LauanMath/kaelix-firmware/docs/referencias.md

# Referências — revisão de literatura do Kaelix

Levantamento gerado por busca sistemática em 5 eixos temáticos, confrontando os
achados numéricos do projeto com a literatura publicada.

> **Estado de verificação.** A etapa de auditoria independente das citações **não
> chegou a rodar** (limite de sessão). A coluna *Meta* traz a confiança auto-declarada
> pelo agente de busca. As entradas marcadas **[CONFERIDO]** foram verificadas por mim
> em fonte primária. Antes de citar qualquer item deste documento na monografia,
> confirme autores, ano e veículo no site do editor ou no DOI.

---

## Verificações em fonte primária

Conferi as citações de maior peso. Duas apresentavam problemas.

### ✅ Vieira, Bauler, Rosa, Silva (2026) — números corrigidos

*Towards a more realistic evaluation of machine learning models for bearing fault
diagnosis.* Mechanical Systems and Signal Processing, v. 258, art. 114640 (no prelo).
Preprint: [arXiv:2509.22267](https://arxiv.org/abs/2509.22267).

**Atenção: há duas versões do artigo com numeração de tabelas diferente.** Verifiquei a
**v1** (set/2025) e o agente de busca leu a **v5** (jul/2026, que é a versão aceita).

Na **v1, Tabela 12** (modelo WDCNN), que eu li diretamente:

| Protocolo no CWRU | Domínio do tempo | Domínio da frequência |
|---|---|---|
| Sem vazamento (*bearing-wise*) | 66,4% ± 16,8% | 62,4% ± 20,6% |
| Vazamento de rolamento (*condition-wise*) | 99,9% ± 0,2% | 100,0% ± 0,0% |
| Vazamento de segmentação | 99,8% ± 0,2% | 99,9% ± 0,1% |

A v1 **não traz p-valores** e **não tem Tabela 13**.

O agente cita a **v5, Tabela 13**: 63,17% ± 10,84% (tempo), 64,34% ± 9,29% (frequência),
63,89% ± 9,26% (envelope) sem vazamento, contra 100,00% ± 0,00% com vazamento
*condition-wise*, e p = 7,11e-8. A v5 reorganizou o artigo (o vazamento virou a Seção 6),
então essa tabela plausivelmente existe — **não consegui confirmá-la** porque o HTML da
v5 veio truncado antes da Seção 6.

**Encaminhamento:** ambas as versões apontam a mesma conclusão — inflação de **33 a 37
pontos percentuais**, contra os 35,8 que medimos (99,0% → 63,2%). Antes de citar na
monografia, **baixe a versão publicada em MSSP** e confirme tabela, valores e p-valor.
Não cite os dois conjuntos de números como se fossem do mesmo lugar.

### ⚠️ El Bouharrouti, Moríñigo-Sotelo, Belahcen (2024) — rótulo invertido

*Multi-Rate Vibration Signal Analysis for Bearing Fault Detection in Induction Machines
Using Supervised Learning Classifiers.* Machines (MDPI), v. 12, n. 1, art. 17.
DOI: 10.3390/machines12010017.

O agente classificou como **"contradiz"** o nosso A1. Li o PDF: **o paper apoia o A1.**
A Figura 7 mostra acurácia baixa a 1 kHz, subindo acentuadamente a partir de 12 kHz, e o
texto afirma que a melhora ocorre "particularmente para sinais cuja taxa é igual ou
superior a 12 kHz". SVM e MNLR "não aprenderam do conjunto de treino" a 1 e 6 kHz. Na
Figura 9, modelos treinados a 1–6 kHz classificam mal os sinais de 48 kHz.

Três ressalvas que **enfraquecem o paper como evidência**, em qualquer direção:

1. **Confundidor de quantidade de dados.** A 1 kHz restam 96 amostras contra 4678 a
   48 kHz (Figura 6). O colapso pode ser escassez de dados, não perda de banda.
2. **Falhas artificiais por eletroerosão**, de 0,178 a 0,533 mm — severas, não
   incipientes. Não testa o caso que nos interessa.
3. **Batches com 50% de sobreposição**, sem split por rolamento — exatamente o
   vazamento que o item A3 identifica. Os valores absolutos são provavelmente inflados.

Usam 20 descritores de domínio do tempo (incluindo curtose e fator de crista) e
**descartaram explicitamente os descritores de frequência**.

### ✅ Demais verificações pontuais

- **ISO 20816-3:2022 e ISO 10816-3:2009** — o agente afirma ter lido o texto normativo e
  cita a exigência de resposta plana em 10–1000 Hz. Plausível e coerente com a ISO 2954,
  mas **não confirmei o texto da norma** (documento pago). Confirme antes de citar.
- **Documentação do scikit-learn** — a afirmação de que `offset_ = -0.5` quando
  `contamination="auto"` é verificável na documentação oficial e sustenta o A4.

---

## Eixo 1 — Isolation Forest, limiar e TinyML embarcado

**Achado confrontado:** A4 · **Veredito da busca:** ALINHADO

| Paper | Ano | Veículo | Relação | Meta |
|---|---|---|---|---|
| Antonini, Pincheira, Vecchio, Antonelli. *An Adaptable and Unsupervised TinyML Anomaly Detection System for Extreme Indust* | 2023 | Sensors (MDPI), 23(4):2344 | confirma | ✓ |
| scikit-learn developers. *sklearn.ensemble.IsolationForest -- documentacao oficial (v1.9 estavel, acessada* | 2026 | Documentacao oficial scikit-learn (fonte prim | confirma | ✓ |
| Liu, Ting, Zhou. *Isolation Forest* | 2008 | IEEE ICDM 2008, pp. 413-422 | matiza | ✓ |
| Ma, Zhao, Zhang, Akoglu. *The Need for Unsupervised Outlier Model Selection: A Review and Evaluation of In* | 2021 | arXiv cs.LG 2104.01422; versao de revista em  | confirma | ✓ |
| Han, Hu, Huang, Jiang, Zhao. *ADBench: Anomaly Detection Benchmark* | 2022 | NeurIPS 2022 (Datasets & Benchmarks Track) | matiza | ✓ |
| Brito, Susto, Brito, Duarte. *An Explainable Artificial Intelligence Approach for Unsupervised Fault Detection* | 2021 | arXiv cs.AI 2102.11848 (versao de revista: Me | confirma | ~ |
| Hermansa, Kozielski, Michalak, Szczyrba, Wrobel, Sikora. *Sensor-Based Predictive Maintenance with Reduction of False Alarms -- A Case Stu* | 2022 | Sensors (MDPI), 22(1):226 | confirma | ✓ |
| Barbariol, Susto. *TiWS-iForest: Isolation forest in weakly supervised and tiny ML scenarios* | 2022 | Information Sciences, 610:126-143 | matiza | ✓ |
| Siffer, Fouque, Termier, Largouet. *Anomaly Detection in Streams with Extreme Value Theory* | 2017 | ACM SIGKDD (KDD) 2017, pp. 1067-1075 | matiza | ✓ |
| Koizumi, Kawaguchi, Imoto, Nakamura, Nikaido, Tanabe, Purohi. *Description and Discussion on DCASE2020 Challenge Task2: Unsupervised Anomalous * | 2020 | DCASE2020 Workshop (arXiv 2006.05822) | matiza | ✓ |
| Bouman, Bukhsh, Heskes. *Unsupervised Anomaly Detection Algorithms on Real-world Data: How Many Do We Nee* | 2024 | Journal of Machine Learning Research, 25(105) | contexto | ✓ |
| Bouman, Heskes. *Autoencoders for Anomaly Detection are Unreliable* | 2025 | arXiv cs.LG 2501.13864 (preprint, sem publica | contexto | ✓ |

<details><summary>Achados detalhados</summary>

**Antonini, Pincheira, Vecchio, Antonelli (2023)** — An Adaptable and Unsupervised TinyML Anomaly Detection System for Extreme Industrial Environments  
`https://doi.org/10.3390/s23042344`  
Trabalho mais proximo do Kaelix: Isolation Forest TREINADO E EXECUTADO no proprio ESP32 (ESP32_WROVER_IE, firmware MicroPython), amostragem de acel+giro a 1125 Hz. Numeros: 84 KB de memoria na inferencia com ensemble de 50 arvores; ~1.570 KB no treino com 30 arvores; carregamento do modelo ate ~1 MB para 50 arvores; latencia de inferencia 20,33 +/- 7,17 ms (instancias normais) e 16,27 +/- 7,04 ms (anomalas); treino on-device 1,2-6,4 s para 10-50 arvores. PONTO CRITICO PARA A4: o limiar de deteccao NAO foi deixado no default -- foi FIXADO MANUALMENTE em 0,75 sobre o score normalizado do Isolation Forest, assumindo que a fase inicial de treino contem apenas comportamento normal. Os autores declaram explicitamente que avaliar a acuracia de deteccao esta fora do escopo do trabalho -- ou seja, nao ha FPR reportado.

**scikit-learn developers (2026)** — sklearn.ensemble.IsolationForest -- documentacao oficial (v1.9 estavel, acessada em ago/2026)  
`https://scikit-learn.org/stable/modules/generated/sklearn.ensemble.IsolationForest.html`  
PROVA MECANICA DIRETA DE A4. Texto literal do atributo offset_: 'decision_function = score_samples - offset_. When the contamination parameter is set to "auto", the offset is equal to -0.5 as the scores of inliers are close to 0 and the scores of outliers are close to -1. When a contamination parameter different than "auto" is provided, the offset is defined in such a way we obtain the expected number of outliers (samples with decision function < 0) in training.' Consequencias: (1) contamination='auto' congela o corte em -0,5, um valor herdado da interpretacao do artigo original, NAO calibrado nos dados -- por isso pode marcar fracao arbitrariamente grande da operacao normal; (2) contamination altera SOMENTE o offset, nunca os scores brutos de score_samples -- logo qualquer metrica baseada em ranking (ROC-AUC) e matematicamente INVARIANTE ao parametro. Isso confirma exatamente o achado 'AUC=1,000 independente do parametro: ele so move o limiar'. Range permitido para float: (0, 0.5].

**Liu, Ting, Zhou (2008)** — Isolation Forest  
`https://doi.org/10.1109/ICDM.2008.17`  
Artigo fundador. Score s(x,n) = 2^(-E(h(x))/c(n)), com c(n) o comprimento medio de caminho em uma BST aleatoria de n nos. s -> 1 indica anomalia; s -> 0 indica normal denso; s ~ 0,5 corresponde a E(h(x)) ~ c(n), ou seja, ponto com profundidade tipica. Os autores usam 0,5 como REFERENCIA INTERPRETATIVA (se toda a amostra devolve s ~ 0,5, o conjunto nao tem anomalia distinta), nao como limiar operacional calibrado -- e exatamente esse 0,5 que o sklearn materializa como offset_=-0,5 no modo 'auto'. Defaults recomendados de ensemble: t=100 arvores, psi=256 (subamostragem), que os autores mostram ser robustos -- a robustez do iForest e nos parametros do ENSEMBLE, nao no limiar.

**Ma, Zhao, Zhang, Akoglu (2021)** — The Need for Unsupervised Outlier Model Selection: A Review and Evaluation of Internal Evaluation Strategies (A Large-scale Study on Unsupervised Outlier Model Selection: Do Internal Strategies Suffice?)  
`https://arxiv.org/abs/2104.01422`  
Responde diretamente a pergunta 'como escolher contamination sem rotulos'. Testbed com 39 tarefas de deteccao, 297 modelos candidatos (8 detectores x varias configuracoes de hiperparametros) e 7 estrategias internas de avaliacao (sem rotulos). Conclusao literal: nenhuma seria 'practically useful, as they select models only comparable to a state-of-the-art detector (with random configuration)'. Ou seja: NAO existe metodo label-free confiavel para escolher detector+hiperparametro; deixar no default e estatisticamente equivalente a sortear -- o que valida a critica de A4 ao contamination='auto' como escolha nao informada.

**Han, Hu, Huang, Jiang, Zhao (2022)** — ADBench: Anomaly Detection Benchmark  
`https://arxiv.org/abs/2206.09426`  
30 algoritmos (14 nao supervisionados, 7 semi-supervisionados, 9 supervisionados) x 57 datasets = 98.436 experimentos. Dois achados diretamente aplicaveis: (1) NENHUM algoritmo nao supervisionado e estatisticamente melhor que os outros -- a escolha do detector importa menos que o protocolo; (2) com apenas 1% de anomalias ROTULADAS, a maioria dos metodos semi-supervisionados ja supera o melhor metodo nao supervisionado. Implicacao pratica para o Kaelix: rotular alguns ensaios de falha (ex.: MAFAULDA) produz mais resultado que otimizar o Isolation Forest puro.

**Brito, Susto, Brito, Duarte (2021)** — An Explainable Artificial Intelligence Approach for Unsupervised Fault Detection and Diagnosis in Rotating Machinery  
`https://arxiv.org/abs/2102.11848`  
11 detectores nao supervisionados comparados (kNN, MCD, LOF, CBLOF, OCSVM, Descritor Bagging, FastABOD, Isolation Forest, HBOS, LODA, Ensemble) em 3 datasets de maquinas rotativas, com descritores de vibracao a 20 kHz (curtose, RMS, BPFI/BPFO/BSF, harmonicos 1x-4x) e explicabilidade via SHAP e Local-DIFFI. Numeros: IF com F1 97,19% e PR-AUC 99,92% (rolamento run-to-failure), F1 99,71% e PR-AUC 99,99% (caixa de engrenagens), F1 97,20% e PR-AUC 99,74% (faltas mecanicas). PONTO CRITICO: o limiar NAO veio de 'auto' -- em condicao estatica a razao de contaminacao era CONHECIDA e usada para definir o limiar; em condicao dinamica o limiar veio da hipotese 'o grupo de treino contem apenas sinais normais'. Alem disso reportam PR-AUC, nao so ROC-AUC.

**Hermansa, Kozielski, Michalak, Szczyrba, Wrobel, S (2022)** — Sensor-Based Predictive Maintenance with Reduction of False Alarms -- A Case Study in Heavy Industry  
`https://doi.org/10.3390/s22010226`  
Melhor evidencia de campo sobre taxa de falso alarme. Comparam HDBSCAN, LOF, Isolation Forest e One-Class SVM em sensores de vibracao (max e RMS) + temperatura de britadores de carvao (NW-10, NW-20) e porticos (S201, S202), mais um dataset sintetico de 30.000 observacoes. Numeros: o detector de outliers ISOLADO produziu metrica de falso positivo N entre 0,457 e 0,939 conforme o conjunto; adicionando adaptacao do modelo base + modelo de correcao, N caiu para 0,026-0,115, uma reducao MEDIA de 90,25% nos falsos alarmes. Ou seja: um detector nao supervisionado 'cru' e inaceitavel em campo, exatamente o cenario de A4.

**Barbariol, Susto (2022)** — TiWS-iForest: Isolation forest in weakly supervised and tiny ML scenarios  
`https://doi.org/10.1016/j.ins.2022.07.129`  
Unico trabalho encontrado que ataca o Isolation Forest especificamente para TinyML/microprocessadores ultra-restritos. Argumento central: 'the standard algorithm might be improved in terms of memory requirements, latency and performances', o que e critico em cenarios de baixo recurso e implementacoes TinyML. A solucao proposta NAO e mexer em contamination, e sim usar supervisao FRACA (poucos rotulos) para ranquear e podar as arvores do ensemble, reduzindo simultaneamente memoria, latencia e erro de deteccao. Codigo publico para reprodutibilidade. Preprint anterior: arXiv 2111.15432 (2021).

**Siffer, Fouque, Termier, Largouet (2017)** — Anomaly Detection in Streams with Extreme Value Theory  
`https://doi.org/10.1145/3097983.3098144`  
Alternativa metodologica principiada ao contamination. Os algoritmos SPOT/DSPOT usam Teoria de Valores Extremos (peaks-over-threshold / distribuicao de Pareto generalizada) para fixar o limiar SEM hipotese sobre a distribuicao dos dados e SEM limiar ajustado a mao. O unico parametro e o RISCO q, que controla diretamente a taxa de falsos positivos -- isto e, o engenheiro especifica o FPR desejado em vez de adivinhar a fracao de anomalias. E exatamente a substituicao que A4 pede para contamination='auto'.

**Koizumi, Kawaguchi, Imoto, Nakamura, Nikaido, Tana (2020)** — Description and Discussion on DCASE2020 Challenge Task2: Unsupervised Anomalous Sound Detection for Machine Condition Monitoring  
`https://arxiv.org/abs/2006.05822`  
Benchmark de referencia para o cenario EXATO do Kaelix: so ha dados normais no treino e as anomalias sao desconhecidas ('detect unknown anomalous sounds under the condition that only normal sound samples have been provided as training data'). 117 submissoes de 40 equipes. PROTOCOLO DE LIMIAR (o que substituir por contamination='auto'): o baseline autoencoder assume que o score de anomalia segue uma distribuicao GAMA, estima os parametros a partir do histograma dos scores dos dados NORMAIS de treino e define o limiar no PERCENTIL 90 dessa gama. Metrica primaria e AUC + pAUC (AUC parcial em faixa de baixa FPR), justamente porque AUC global sozinha nao caracteriza o ponto de operacao.

</details>

**Números citáveis:** MECANISMO (scikit-learn, doc oficial v1.9): contamination='auto' => offset_ = -0.5; decision_function = score_samples - offset_; float permitido apenas em (0, 0.5]; contamination redefine SO o offset, nunca score_samples => ROC-AUC invariante. | LIU/TING/ZHOU 2008 (ICDM, pp. 413-422): s(x,n)=2^(-E(h(x))/c(n)); s~0.5 <=> E(h(x))~c(n); defaults de ensemble t=100 arvores, psi=256 subamostras. | ANTONINI 2023 (Sensors 23(4):2344, ESP32 + IF em MicroPython): amostragem 1125 Hz; 84 KB de RAM na inferencia com 50 arvores; ~1.570 KB no treino com 30 arvores; carregamento de modelo ate ~1 MB (50 arvores); latencia 20,33 +/- 7,17 ms (normal) e 16,27 +/- 7,04 ms (anomalo); treino on-device 1,2-6,4 s (10-50 arvores); LIMIAR FIXADO EM 0,75 do score normalizado. | HERMANSA 2022 (Sensors 22(1):226): detector isolado com metrica de FP N = 0,457-0,939; com adaptacao+correcao N = 0,026-0,115; reducao media de falsos alarmes de 90,25%; dataset sintetico de 30.000 observacoes. | BRITO/SUSTO (MSSP 163:108105 / arXiv 2102.11848): 11 detectores; sinais a 20 kHz; IF F1 97,19% e PR-AUC 99,92% (rolamento), F1 99,71% e PR-AUC 99,99% (engrenagens), F1 97,20% e PR-AUC 99,74% (faltas mecanicas). | MA/AKOGLU: 39 tarefas, 297 modelos, 8 detectores, 7 estrategias internas, ZERO melhores que configuracao aleatoria. | ADBENCH (NeurIPS 2022): 30 algoritmos, 57 datasets, 98.436 experimentos; nenhum nao supervisionado estatisticamente superior; 1% de rotulos ja basta para semi-supervisionado bater o melhor nao supervisionado. | BOUMAN JMLR 2024, 25(105):1-34: 33 algoritmos x 52 datasets, EIF vence significativamente. | DCASE2020 Task 2 (Koizumi et al.): limiar = percentil 90 de uma GAMA ajustada aos scores dos dados normais de treino; metrica primaria AUC + pAUC (AUC parcial em faixa de baixa FPR); 117 submissoes de 40 equipes. | SIFFER KDD 2017 (pp. 1067-1075): SPOT/DSPOT via EVT, unico parametro = risco q que controla diretamente a taxa de falsos positivos. | REFERENCIA DE GESTAO DE ALARME (fonte NAO academica, verificar antes de citar): EEMUA 191 -- media recomendada de ~6 alarmes/hora por operador e pico de no maximo 10 alarmes por 10 minutos (inicio de 'alarm flood'); util para argumentar que 42% de janelas normais marcadas como anomalia e ordens de grandeza acima do tolerável.

**Lacunas neste eixo:** 1) NUMERO ORIGINAL SEM PRECEDENTE NA LITERATURA: nao encontrei nenhum trabalho que quantifique a FRACAO da operacao normal marcada como anomalia por contamination='auto' em vibracao industrial. Os 42% de voces parecem ser contribuicao original -- otimo para o TCC, mas exige que a metodologia (dataset, descritores, split) seja descrita com muito rigor, porque nao ha baseline publicado para comparar. 2) O trabalho mais proximo (Antonini et al., IF em ESP32) declara EXPLICITAMENTE que avaliar acuracia de deteccao esta fora do escopo -- ou seja, nao existe FPR publicado para Isolation Forest embarcado em MCU. Isso e um buraco que o Kaelix pode preencher. 3) Ninguem cruza as duas restricoes de voces ao mesmo tempo: acelerometro MEMS de banda limitada (MPU6050, Nyquist 500 Hz) + detector nao supervisionado embarcado + limiar calibrado para um FPR alvo. A literatura de vibracao usa 20-50 kHz (Brito: 20 kHz; MAFAULDA: 50 kHz), e a literatura TinyML usa banda baixa mas sem discutir o custo diagnostico dessa escolha (conexao direta com o achado A1 de voces). 4) NAO EXISTE NORMA que fixe taxa de falso alarme aceitavel para manutencao preditiva por vibracao: ISO 10816/20816 define severidade de VELOCIDADE, nao estatistica de alarme; EEMUA 191 e ISA-18.2 sao de alarmes de processo, nao de PdM. Qualquer numero de FPR aceitavel que voces adotarem precisa ser justificado por custo (razao custo de falso negativo : falso positivo, tipicamente citada como 20:1 a 100:1 em fontes de industria -- mas so achei isso em fontes NAO academicas, nao citem sem verificar). 5) Falta comparacao controlada IF vs OC-SVM vs autoencoder EM MCU com o MESMO orcamento de memoria E o MESMO protocolo de limiar; os papers comparam ou algoritmos (em PC) ou plataformas (sem controlar o limiar). 6) Nenhuma das bibliotecas de exportacao sklearn->C mais usadas (emlearn, micromlgen) documenta suporte a IsolationForest -- so a arvores/RF/SVM/NB; Antonini et al. contornaram isso implementando o IF diretamente em MicroPython. Se voces pretendem embarcar o IF, isso e um risco de implementacao que a literatura nao cobre e que vale registrar. 7) Nao encontrei nada sobre DERIVA (concept drift) do limiar do IF em motor industrial ao longo de meses -- carga, temperatura e regime mudam o score base, e nenhum dos papers de MCU faz recalibracao periodica.

---

## Eixo 2 — Vazamento de dados e avaliação em datasets de rolamento

**Achado confrontado:** A3 · **Veredito da busca:** ALINHADO

| Paper | Ano | Veículo | Relação | Meta |
|---|---|---|---|---|
| Vieira, Bauler, Rosa, Silva. *Towards a more realistic evaluation of machine learning models for bearing fault* | 2026 | Mechanical Systems and Signal Processing, v.  | confirma | ✓ |
| Hendriks, Dumond, Knox. *Towards better benchmarking using the CWRU bearing fault dataset* | 2022 | Mechanical Systems and Signal Processing, v.  | confirma | ✓ |
| Varejão, Costa, Silva, Rodrigues, Ribeiro, Varejão, Oliveira. *The similarity bias problem: What it is and how it impacts vibration based intel* | 2025 | Mechanical Systems and Signal Processing, v.  | confirma | ✓ |
| Wheat, von Mohrenschildt, Habibi, Al-Ani. *Impact of Data Leakage in Vibration Signals Used for Bearing Fault Diagnosis* | 2024 | IEEE Access, v. 12, p. 169879-169895 | confirma | ✓ |
| Abburi, Chaudhary, Ilyas, Manne, Mittal, Williams, Snaidauf,. *A Closer Look at Bearing Fault Classification Approaches* | 2023 | Annual Conference of the PHM Society, v. 15 ( | matiza | ✓ |
| Rauber, Loca, Boldt, Rodrigues, Varejão. *An experimental methodology to evaluate machine learning methods for fault diagn* | 2021 | Expert Systems with Applications, v. 167, art | confirma | ✓ |
| Matania, Cohen, Bechhoefer, Bortman. *Test-Training Leakage in Evaluation of Machine Learning Algorithms for Condition* | 2024 | PHM Society European Conference, v. 8, n. 1,  | confirma | ✓ |
| Knap, Jachymczyk, Lalik. *Leakage-Safe, Reproducible Benchmarking for Vibration-Based Fault Diagnosis* | 2026 | PHM Society European Conference, v. 9, n. 1 | confirma | ✓ |
| Smith, Randall. *Rolling element bearing diagnostics using the Case Western Reserve University da* | 2015 | Mechanical Systems and Signal Processing, v.  | contexto | ✓ |
| Zhao, Li, Wu, Sun, Wang, Yan, Chen. *Deep learning algorithms for rotating machinery intelligent diagnosis: An open s* | 2020 | ISA Transactions, v. 107, p. 224-255 | matiza | ✓ |
| Fan, Jiang, Zhang, Zheng, Lv, Han, Liang, Li, Zhang, Qian, C. *FISHER: A Foundation Model for Multi-Modal Industrial Signal Comprehensive Repre* | 2026 | IEEE Transactions on Industrial Informatics ( | confirma | ~ |
| Shamim, Nuruzzaman, Ferdus, Ahmed, Anward, Tooneer, Khan, Ho. *Leakage-Robust Evaluation and Data-Scale Sensitivity of Attention-Enhanced Multi* | 2026 | arXiv (submetido a Next Research, Elsevier) | confirma | ✓ |

<details><summary>Achados detalhados</summary>

**Vieira, Bauler, Rosa, Silva (2026)** — Towards a more realistic evaluation of machine learning models for bearing fault diagnosis  
`https://doi.org/10.1016/j.ymssp.2026.114640 (preprint: https://arxiv.org/abs/2509.22267)`  
Paper-espelho do nosso A3, com numeros quase identicos. Experimento controlado (treino FIXO, so o conjunto de teste muda, eliminando o confundidor 'menos dados de treino'). CWRU: protocolo sem vazamento da Macro AUROC 63,17% +/- 10,84% (tempo), 64,34% +/- 9,29% (frequencia), 63,89% +/- 9,26% (envelope); com vazamento de nivel de rolamento (split condition-wise) sobe para 100,00% +/- 0,00%, 99,96% +/- 0,13% e 99,79% +/- 0,54%; com vazamento de segmentacao, 100,00% nos tres casos (p entre 7,1e-8 e 1,7e-8). PU: sem vazamento 54,25% +/- 17,79% (tempo) / 61,25% (freq) / 76,98% (envelope); condition-wise +32,6 p.p. (86,88%/92,27%/87,79%); repetition-wise 98,57%/100,00%/99,99% (+44,3 p.p.); segmentacao 98,56%/100%/100%. UORED-VAFCLS: sem vazamento 87,25%/90,21%/87,34%; vazamento de rolamento +3,0/+3,9/+6,4 p.p.; vazamento de segmentacao +12,6/+9,8/+12,5 p.p. (chega a 99,88%/100,00%/99,88%). Taxonomia formal: 'segmentation-level leakage' vs 'bearing-level leakage' (este ultimo com sub-tipos condition-wise e repetition-wise). Survey: 195 artigos MSSP de 2025 recuperados, 18 analisados em detalhe - 8 (44%) usaram split aleatorio, 9 (50%) condition-wise, 1 (6%) nao especificou; citam trabalhos anteriores que reportam problemas de particao em >90% dos artigos publicados. Toy problem com 48 rolamentos: teto teorico de acuracia 90,30%, e os testes com vazamento EXCEDERAM esse teto (prova de memorizacao). NUANCE CRITICA PARA NOS: sob split correto no CWRU (Tabela 10), o Random Forest com descritores de tempo+envelope chegou a 85,06% +/- 8,92% Macro AUROC, contra 63,22% +/- 10,24% do WDCNN - modelos rasos degradam MENOS que deep learning sob particao honesta. Outra ressalva: no experimento CWRU eles tiveram de EXCLUIR todos os sinais saudaveis, pois o CWRU tem uma unica configuracao de rolamento saudavel e nao ha como fazer split bearing-wise da classe normal.

**Hendriks, Dumond, Knox (2022)** — Towards better benchmarking using the CWRU bearing fault dataset  
`https://doi.org/10.1016/j.ymssp.2021.108732`  
Paper-semente da critica moderna ao CWRU (158 citacoes no Semantic Scholar). Argumenta que o procedimento aceito de montar treino e teste com CONDICOES DE OPERACAO diferentes (0/1/2/3 hp) NAO constitui um problema real de domain shift, porque os MESMOS rolamentos fisicos aparecem nos dois conjuntos. Propoe um framework alternativo de benchmark que constroi treino e teste com conjuntos INDEPENDENTES de rolamentos. E a origem da distincao 'variacao de condicao != variacao de componente' que sustenta o nosso A3. Limitacao apontada por Vieira et al. (2026): a estrategia por tamanho de falha de Hendriks nao elimina o vazamento da classe saudavel, que continua sendo dividida por carga.

**Varejão, Costa, Silva, Rodrigues, Ribeiro, Varejão (2025)** — The similarity bias problem: What it is and how it impacts vibration based intelligent fault diagnosis  
`https://doi.org/10.1016/j.ymssp.2025.112822`  
Cunha o termo 'similarity bias' para o fenomeno que chamamos de vazamento por janela. Levantamento sistematico: de 41 estudos revisados que usam o CWRU (publicados entre 2008 e 2020), 40 empregaram desenho experimental suscetivel a esse vies - ou seja, ~97,6% da literatura CWRU daquele periodo e otimista por construcao. Compara modelos convencionais e de deep learning sob estrategia de validacao cruzada que controla o vies, e mostra quantitativamente que o similarity bias produz resultados otimistas. Grupo brasileiro (UFES), mesmo grupo do Rauber et al. (2021) que usa MAFAULDA - terminologia util e citavel em portugues/ingles.

**Wheat, von Mohrenschildt, Habibi, Al-Ani (2024)** — Impact of Data Leakage in Vibration Signals Used for Bearing Fault Diagnosis  
`https://doi.org/10.1109/ACCESS.2024.3497716`  
Quantifica o vazamento com metodos SEM modelo treinado pesado - exatamente o regime do KAELIX. Aplica 6 metodos classicos de diagnostico (PCA, SPCA e LDA combinados com analise em frequencia e analise de envelope) a 2 datasets (McMaster e Paderborn) sob 3 estrategias de particao: run-to-run, day-to-day e part-to-part. Reporta variacoes de desempenho SUPERIORES A 40 PONTOS PERCENTUAIS de acuracia dependendo apenas da estrategia de particao, expondo domain shifts nao identificados anteriormente (inclusive shift entre DIAS de aquisicao, nao so entre pecas). Recomenda protocolos melhores de desenho experimental e avaliacao. A nomenclatura run-to-run / day-to-day / part-to-part e mais granular que o nosso 'split por ensaio' e vale adotar.

**Abburi, Chaudhary, Ilyas, Manne, Mittal, Williams, (2023)** — A Closer Look at Bearing Fault Classification Approaches  
`https://arxiv.org/abs/2309.17001 | https://papers.phmsociety.org/index.php/phmconf/article/view/3473`  
Fonte de numeros diretos e NUANCE IMPORTANTE contra a magnitude do nosso A3. Classificacao multiclasse no CWRU, comparando split por rolamento vs split aleatorio: SVM+STFT cai de 0,851 (aleatorio) para 0,700 (por rolamento) de acuracia; Naive Bayes+RFFT cai de 0,858 para 0,695. No XJTU: SVM+STFT 0,988 -> 0,890; NB+RFFT 0,910 -> 0,728. Ou seja, a queda observada por eles no CWRU e de ~15 p.p., NAO ~36 p.p. como no nosso A3. Alertam explicitamente que estudos anteriores (citam nominalmente Zhao et al. 2020) usaram split aleatorio atribuindo registros do MESMO rolamento a treino, validacao e teste. Tambem defendem F-score/metricas de desbalanceamento em vez de acuracia pura, e o uso de dummy classifiers como baseline - recomendacao diretamente aplicavel ao nosso relatorio.

**Rauber, Loca, Boldt, Rodrigues, Varejão (2021)** — An experimental methodology to evaluate machine learning methods for fault diagnosis based on vibration signals  
`https://doi.org/10.1016/j.eswa.2020.114022`  
UNICO paper de metodologia de avaliacao encontrado que usa explicitamente MAFAULDA E CWRU juntos - exatamente a nossa combinacao de datasets. Estabelece um procedimento sistematico para comparar de forma justa scores experimentais de metodos de ML sobre sinais de vibracao. Afirma que o desenho experimental da maioria das publicacoes da area e enviesado, baseado em metodos de validacao inaceitavelmente simples e na reciclagem de padroes identicos no conjunto de teste que ja foram usados no treino, o que torna a classificacao uma tarefa facil. E uma das duas fontes (junto com Varejão et al. 2025) das quais Vieira et al. (2026) tiram a estatistica de problemas de particao em >90% dos artigos publicados. 93 citacoes.

**Matania, Cohen, Bechhoefer, Bortman (2024)** — Test-Training Leakage in Evaluation of Machine Learning Algorithms for Condition-Based Maintenance  
`https://doi.org/10.36001/phme.2024.v8i1.4125`  
Artigo curto e didatico, dedicado exclusivamente ao problema: em muitos trabalhos de ML para manutencao baseada em condicao, especialmente classificacao de falhas de rolamento, a separacao de exemplos entre teste e treino esta incorreta, levando a conclusao otimista sobre o desempenho do algoritmo quando o desempenho real e menor. Propoe divisao guiada por TAMANHO DE FALHA (fault-size guided splitting) aplicada a CWRU e PU. Ressalva registrada por Vieira et al. (2026): essa estrategia nao e aplicavel a datasets em que o mesmo rolamento aparece sob multiplos tamanhos de falha (ex.: UORED-VAFCLS), e no CWRU ela nao resolve a classe saudavel. Util como citacao curta e de autoridade (Bechhoefer e referencia em PHM industrial).

**Knap, Jachymczyk, Lalik (2026)** — Leakage-Safe, Reproducible Benchmarking for Vibration-Based Fault Diagnosis  
`https://doi.org/10.36001/phme.2026.v9i1.4924`  
Benchmark reprodutivel e livre de vazamento para diagnostico cross-domain, com codigo aberto (github.com/1Sensor/pdm-bench). Afirma que particao em nivel de JANELA e cenarios fonte-alvo mal definidos levam a conclusoes excessivamente otimistas. Define 6 cenarios fonte-alvo fixos com separacao treino-teste em NIVEL DE GRAVACAO (recording-level) sobre CWRU e Paderborn. Achado que nos e util como nuance: a dificuldade dos cenarios e altamente heterogenea - alguns cenarios de transferencia estao efetivamente saturados enquanto outros permanecem substancialmente mais dificeis. Isso sugere que reportar um unico numero medio (como nosso 63,2% +/- 19,2%) esconde variancia estrutural, e que o desvio-padrao alto que observamos e esperado. Tambem nota que modelos de deep learning frequentemente atingem desempenho superior mas suas conclusoes sao sensiveis a inicializacao.

**Smith, Randall (2015)** — Rolling element bearing diagnostics using the Case Western Reserve University data: A benchmark study  
`https://doi.org/10.1016/j.ymssp.2015.04.021`  
Critica FUNDACIONAL ao CWRU, anterior a discussao de ML, com 2443 citacoes. Aplica tres tecnicas classicas de diagnostico a TODO o dataset CWRU e classifica cada registro em categorias de diagnosticabilidade: Y1 (claramente diagnosticavel com caracteristicas classicas no tempo e na frequencia), Y2 (claramente diagnosticavel mas com caracteristicas nao-classicas), P1 (provavelmente diagnosticavel - componentes discretos nas frequencias de falha esperadas mas nao dominantes no espectro de envelope), P2 (potencialmente diagnosticavel - componentes borrados que parecem coincidir com as frequencias esperadas), N1 (nao diagnosticavel para a falha especificada, mas com outros problemas identificaveis como folga/looseness) e N2 (nao diagnosticavel e praticamente indistinguivel de ruido). Consequencia direta para nos: parte dos registros CWRU e ROTULADA como falha mas nao contem assinatura de falha detectavel - portanto uma acuracia de 99% em split aleatorio e literalmente impossivel por via fisica, o que e evidencia independente de que aquele numero e memorizacao. Fornece recomendacoes de como usar os dados para testar novos algoritmos.

</details>

**Números citáveis:** NUMEROS DIRETAMENTE CITAVEIS (todos extraidos de fonte primaria aberta e conferidos):

--- Vieira, Bauler, Rosa & Silva, MSSP v.258, art. 114640 (2026) --- espinha dorsal da nossa argumentacao
CWRU, Tabela 13 (experimento controlado, treino fixo, so o teste muda), Macro AUROC:
  sem vazamento: 63,17% +/- 10,84% (tempo) | 64,34% +/- 9,29% (frequencia) | 63,89% +/- 9,26% (envelope)
  vazamento de nivel de rolamento (condition-wise): 100,00% +/- 0,00% | 99,96% +/- 0,13% | 99,79% +/- 0,54%
  vazamento de segmentacao: 100,00% | 100,00% | 100,00%
  p-valores (teste t pareado unicaudal): 7,11e-8 | 1,93e-8 a 2,02e-8 | 1,88e-8 a 1,70e-8
PU, Tabela 12, Macro AUROC:
  sem vazamento: 54,25% +/- 17,79% | 61,25% +/- 17,96% | 76,98% +/- 8,51%
  condition-wise: 86,88% +/- 14,55% | 92,27% +/- 11,80% | 87,79% +/- 18,50%  (ganho de 32,6 p.p. no dominio do tempo)
  repetition-wise: 98,57% +/- 2,15% | 100,00% +/- 0,00% | 99,99% +/- 0,01%   (ganho de 44,3 p.p. no dominio do tempo)
  segmentacao: 98,56% +/- 2,16% | 100,00% | 100,00% +/- 0,01%
UORED-VAFCLS, Tabela 11, Macro AUROC:
  sem vazamento: 87,25% +/- 6,03% | 90,21% +/- 5,57% | 87,34% +/- 7,71%
  vazamento de rolamento: +3,0 / +3,9 / +6,4 p.p. -> 90,23% | 94,15% | 93,79%
  vazamento de segmentacao: +12,6 / +9,8 / +12,5 p.p. -> 99,88% +/- 0,39% | 100,00% +/- 0,00% | 99,88% +/- 0,39%
CWRU sob protocolo correto, Tabela 10 (Macro AUROC) - NUMERO-CHAVE PARA DEFENDER MODELOS RASOS:
  WDCNN tempo 63,22% +/- 10,24% | WDCNN frequencia 70,90% +/- 8,95% | WDCNN envelope 74,51% +/- 9,43%
  Random Forest (tempo + espectro de envelope) 85,06% +/- 8,92% | SVM 81,06% +/- 6,76%
Survey de prevalencia: 195 artigos MSSP de 2025 recuperados; 18 analisados; 8 (44%) split aleatorio; 9 (50%) condition-wise; 1 (6%) nao especificado.
Toy problem: 48 rolamentos simulados, 24 saudaveis / 24 com falha, 40 amostras por rolamento, 3 descritores preditivas + 48 descritores de identidade (51 no total); teto teorico de acuracia = 90,30%; testes com vazamento EXCEDERAM esse teto.
Numero de sinais de treino nos experimentos: ~24 (UORED), ~700 (PU), apenas 3 (CWRU); overlap de 75%, 0% e 95% respectivamente.
Codigo: github.com/gama-ufsc/bearing-data-leakage

--- Abburi et al., PHM Society Conference v.15 (2023) --- a faixa BAIXA da queda
CWRU multiclasse, acuracia (split por rolamento vs split aleatorio):
  SVM + STFT: 0,700 vs 0,851  (F-macro 0,658 vs 0,865)
  Naive Bayes + RFFT: 0,695 vs 0,858  (F-macro 0,693 vs 0,833)
XJTU multiclasse:
  SVM + STFT: 0,890 vs 0,988 | Naive Bayes + RFFT: 0,728 vs 0,910

--- Wheat, von Mohrenschildt, Habibi & Al-Ani, IEEE Access v.12, p.169879-169895 (2024) ---
Variacoes de desempenho SUPERIORES A 40 PONTOS PERCENTUAIS de acuracia dependendo apenas da metodologia de particao. 6 metodos (PCA, SPCA, LDA x analise de frequencia e de envelope), 2 datasets (McMaster, Paderborn), 3 particoes (run-to-run, day-to-day, part-to-part).

--- Varejão et al., MSSP v.235, art. 112822 (2025) ---
40 de 41 estudos revisados que usam CWRU (2008-2020) empregaram desenho experimental suscetivel a similarity bias (~97,6%).

--- Rauber et al. (2021) + Varejão et al. (2025), via Vieira et al. ---
Problemas de particao de dados em MAIS DE 90% dos artigos publicados na area.

--- Shamim et al., arXiv:2607.16493 (2026) --- corroboracao secundaria
Split ingenuo infla a acuracia de 20-60% genuinos para 99,9%. C-MAPSS com 19.976 janelas livres de vazamento: 84,12% +/- 0,96%.

--- MAFAULDA, pagina oficial UFRJ (verificada) --- para a secao de materiais e para a ameaca a validade
1951 sequencias | 50 kHz | 5 s por amostra (250.000 pontos) | 8 canais (1 tacometro, 6 acelerometros IMI 601A01 e 604B31 em underhang e overhang com 3 eixos cada, 1 microfone) | 737 a 3686 rpm (passos de ~60 rpm), ou seja 12,3 a 61,4 Hz de frequencia de eixo.
Distribuicao de classes: normal 49 | desalinhamento horizontal 197 | desalinhamento vertical 301 | desbalanceamento 333 | falha de rolamento underhang 558 | falha de rolamento overhang 513.
APENAS 3 ROLAMENTOS DEFEITUOSOS (um por elemento: pista externa, esferas/gaiola, pista interna) em 2 posicoes; massas adicionais de 0, 6, 20 e 35 g; desbalanceamento 6-35 g; desalinhamento 0,5-2,0 mm (horizontal) e 0,51-1,90 mm (vertical).

--- Smith & Randall, MSSP v.64-65, p.100-131 (2015) --- 2443 citacoes
Categorias de diagnosticabilidade de cada registro CWRU: Y1, Y2 (diagnosticavel), P1, P2 (parcial), N1, N2 (nao diagnosticavel; N2 = indistinguivel de ruido).

--- Contagens de citacao (Semantic Scholar, ago/2026), uteis para justificar escolha de referencias ---
Smith & Randall 2015: 2443 | Zhao et al. 2020: 301+ | Hendriks et al. 2022: 158 | Rauber et al. 2021: 93 | Wheat et al. 2024: 8 | Varejão et al. 2025: 4

**Lacunas neste eixo:** 1) VAZAMENTO EM DETECCAO NAO-SUPERVISIONADA DE ANOMALIA: toda a literatura de vazamento encontrada trata de classificacao SUPERVISIONADA. Nao localizei nenhum paper que analise vazamento de dados em one-class / Isolation Forest / autoencoder para rolamentos. Como o KAELIX combina Isolation Forest (A4) com particao por grupo (A3), essa interacao nao tem precedente direto - o que e simultaneamente uma lacuna e uma oportunidade de contribuicao original do TCC. Em particular, ninguem discute que treinar o detector so em 'normal' e depois particionar por rolamento e impossivel no CWRU (unica configuracao saudavel) e no MAFAULDA (49 sequencias normais de uma unica montagem).

2) O CWRU NAO PERMITE SPLIT LIMPO DA CLASSE SAUDAVEL: Vieira et al. tiveram de EXCLUIR completamente os sinais saudaveis do experimento de vazamento no CWRU (Secao 6.3), porque o dataset contem uma unica configuracao de rolamento saudavel. Isso significa que nenhum protocolo GroupKFold no CWRU consegue ser honesto na tarefa binaria normal-vs-falha, que e exatamente a tarefa do KAELIX. Hendriks (2022) e Abburi (2023) tambem falham nesse ponto especifico. Nao existe solucao publicada - so a alternativa de usar outro dataset.
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
