LauanMath/kaelix-firmware/docs/relatorio/praticas-sistemas-criticos.pdf

# Práticas de tolerância a falhas em sistemas embarcados críticos

# Redundância aviônica, normas de garantia e aplicabilidade ao Kaelix

Documento de referência — projeto Kaelix, Engenharia de Software (ICEV)

# 1 Escopo e critério de leitura

- Unidade da tabela: mecanismo, não norma. Uma norma aparece como origem de vários mecanismos.
- A coluna Limite conhecido registra o que o mecanismo comprovadamente não cobre. Sem ela, a tabela viraria lista de recomendações.
- A coluna Situação no Kaelix admite quatro valores: adotado, parcial, ausente, n/a (não aplicável à classe do sistema).
- Aviônica civil e automotivo entram como origem documentada de prática, não como alvo de certificação. O Kaelix é protótipo acadêmico; nenhum processo de certificação é reivindicado.
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
