LauanMath/kaelix-firmware/hardware/involucro/v1/montagem-corte.step

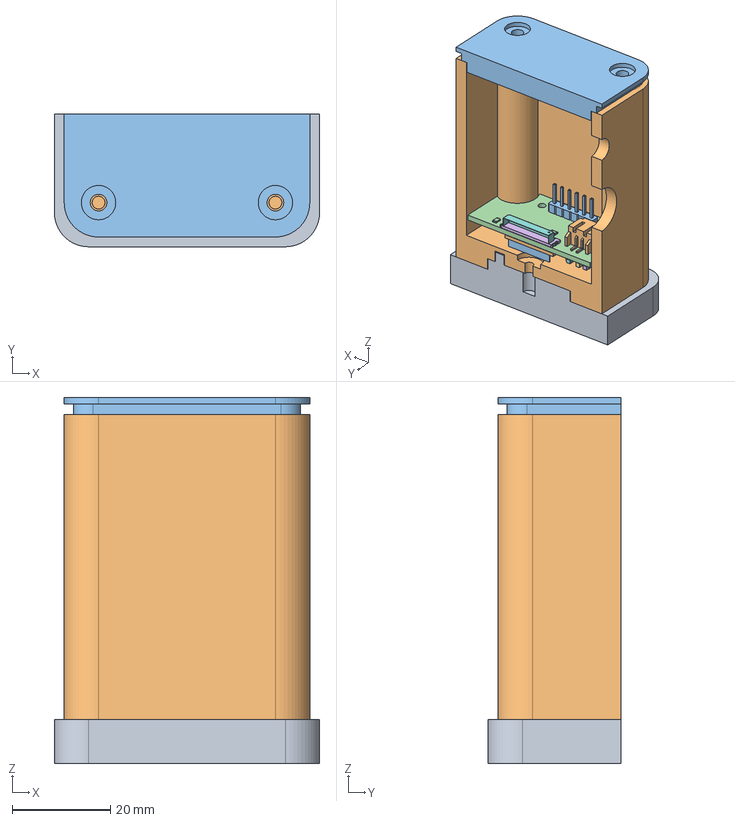
[picture p26: CAD file, 2026-09-28, an earlier design]
hardware/involucro/v1/montagem-corte.step
54.0 x 27.0 x 74.5 mm
