LauanMath/kaelix-firmware/experiments/figures/output/fig5_topologia.pdf

nó

nó

nó

nó

nó

nó

? | ESP32
servidor
A Atual | B Gateway ESP32
C Gateway SBC | D LoRaWAN
sem receptor | 1 canal · sem downlink

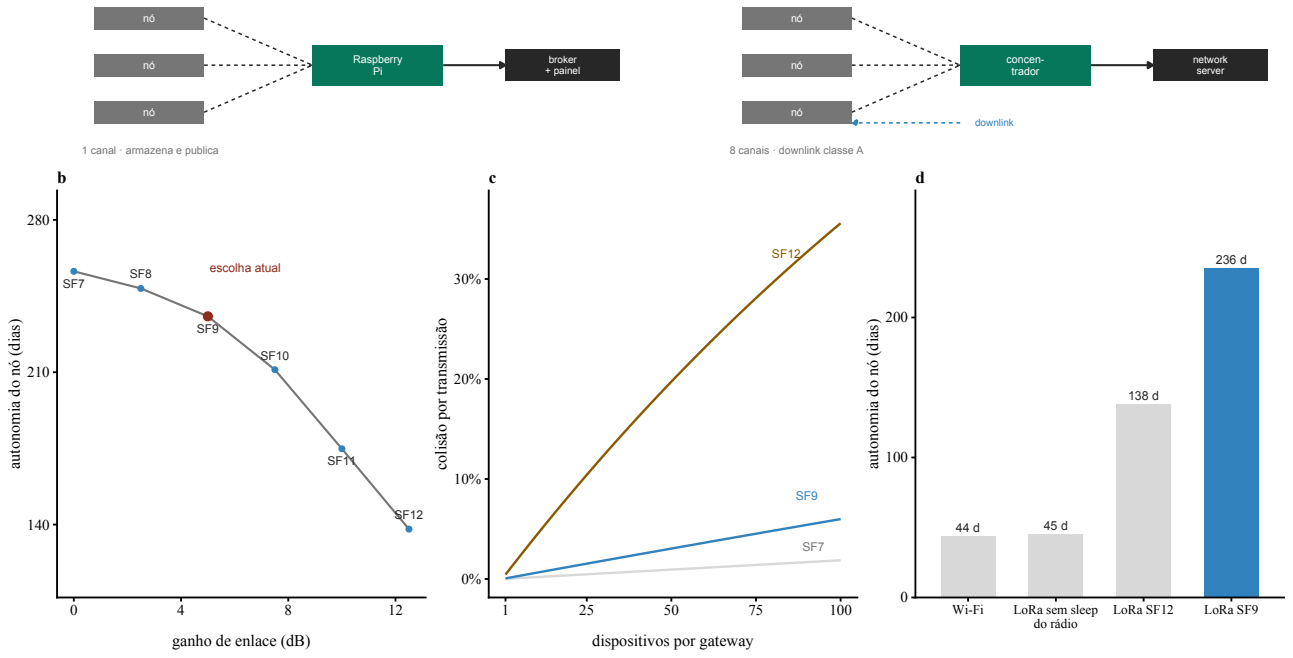
[picture p53: figure]
downlink; Raspberry Pi; concen- trador; broker + painel; network server; escolha atual; ganho de enlace (dB); autonomia do nó (dias); dispositivos por gateway; colisão por transmissão; LoRa sem sleep; do rádio; LoRa SF12; LoRa SF9

1 canal · armazena e publica | 8 canais · downlink classe A

a
