LauanMath/kaelix-firmware/experiments/figures/data/fig10_referencias.csv

classe_iso | v_ab | v_bc | v_cd | zeta_asa | b_sn | n_ref | fn_v1 | fn_v2
III | 1.8 | 4.5 | 11.2 | 0.03 | 6.4 | 20000000.0 | 2001 | 1352
