LauanMath/kaelix-firmware/experiments/figures/data/fig10_transmissibilidade.csv

versao | carga | f_chassi_hz | freq_hz | t
v1 | carga no topo | 936 | 100 | 1.0115
v1 | carga no topo | 936 | 100.59 | 1.0117
v1 | carga no topo | 936 | 101.18 | 1.0118
v1 | carga no topo | 936 | 101.77 | 1.012
v1 | carga no topo | 936 | 102.37 | 1.0121
v1 | carga no topo | 936 | 102.97 | 1.0123
v1 | carga no topo | 936 | 103.58 | 1.0124
v1 | carga no topo | 936 | 104.19 | 1.0125
v1 | carga no topo | 936 | 104.8 | 1.0127
v1 | carga no topo | 936 | 105.41 | 1.0128
v1 | carga no topo | 936 | 106.03 | 1.013
v1 | carga no topo | 936 | 106.66 | 1.0132
v1 | carga no topo | 936 | 107.28 | 1.0133
v1 | carga no topo | 936 | 107.91 | 1.0135
v1 | carga no topo | 936 | 108.55 | 1.0136
v1 | carga no topo | 936 | 109.18 | 1.0138
v1 | carga no topo | 936 | 109.83 | 1.014
v1 | carga no topo | 936 | 110.47 | 1.0141
v1 | carga no topo | 936 | 111.12 | 1.0143
v1 | carga no topo | 936 | 111.77 | 1.0145
v1 | carga no topo | 936 | 112.43 | 1.0146
v1 | carga no topo | 936 | 113.09 | 1.0148
v1 | carga no topo | 936 | 113.75 | 1.015
v1 | carga no topo | 936 | 114.42 | 1.0152
v1 | carga no topo | 936 | 115.09 | 1.0154
v1 | carga no topo | 936 | 115.77 | 1.0155
v1 | carga no topo | 936 | 116.45 | 1.0157
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
