LauanMath/kaelix-firmware/experiments/figures/data/fig11_correcao.csv

t_carcaca | modelo | t_interna
40.0 | concentrado, 500 iterações | 33.306
40.0 | concentrado, convergido | 30.686
42.5 | concentrado, 500 iterações | 34.085
42.5 | concentrado, convergido | 30.844
45.0 | concentrado, 500 iterações | 34.852
45.0 | concentrado, convergido | 30.999
47.5 | concentrado, 500 iterações | 35.610
47.5 | concentrado, convergido | 31.151
50.0 | concentrado, 500 iterações | 36.359
50.0 | concentrado, convergido | 31.302
52.5 | concentrado, 500 iterações | 37.100
52.5 | concentrado, convergido | 31.451
55.0 | concentrado, 500 iterações | 37.833
55.0 | concentrado, convergido | 31.598
57.5 | concentrado, 500 iterações | 38.560
57.5 | concentrado, convergido | 31.744
60.0 | concentrado, 500 iterações | 39.280
60.0 | concentrado, convergido | 31.888
62.5 | concentrado, 500 iterações | 39.994
62.5 | concentrado, convergido | 32.031
65.0 | concentrado, 500 iterações | 40.702
65.0 | concentrado, convergido | 32.173
67.5 | concentrado, 500 iterações | 41.405
67.5 | concentrado, convergido | 32.314
70.0 | concentrado, 500 iterações | 42.102
70.0 | concentrado, convergido | 32.454
72.5 | concentrado, 500 iterações | 42.794
72.5 | concentrado, convergido | 32.593
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
