LauanMath/kaelix-firmware/experiments/figures/data/fig11_perfil.csv

versao | z_mm | t_media | t_min | t_max
v1 | 0.63 | 55.145 | 41.754 | 90.000
v1 | 1.89 | 58.106 | 43.066 | 90.000
v1 | 3.16 | 59.624 | 43.382 | 90.000
v1 | 4.42 | 56.059 | 43.515 | 78.231
v1 | 5.68 | 53.497 | 43.399 | 74.201
v1 | 6.94 | 52.658 | 43.019 | 68.076
v1 | 8.21 | 51.278 | 42.458 | 63.559
v1 | 9.47 | 49.545 | 41.716 | 59.665
v1 | 10.73 | 50.589 | 43.006 | 57.199
v1 | 12.00 | 49.909 | 42.270 | 55.332
v1 | 13.26 | 48.728 | 41.475 | 54.278
v1 | 14.52 | 47.628 | 40.225 | 53.434
v1 | 15.78 | 47.783 | 39.272 | 53.113
v1 | 17.05 | 47.697 | 38.786 | 53.016
v1 | 18.31 | 40.714 | 37.826 | 45.079
v1 | 19.57 | 39.247 | 36.987 | 42.948
v1 | 20.83 | 38.089 | 36.108 | 41.130
v1 | 22.10 | 36.938 | 35.549 | 39.899
v1 | 23.36 | 35.997 | 34.922 | 38.503
v1 | 24.62 | 35.310 | 34.236 | 37.552
v1 | 25.89 | 34.613 | 33.668 | 36.677
v1 | 27.15 | 34.105 | 33.164 | 35.877
v1 | 28.41 | 33.563 | 32.727 | 35.101
v1 | 29.67 | 33.061 | 32.353 | 34.462
v1 | 30.94 | 32.759 | 32.032 | 34.022
v1 | 32.20 | 32.413 | 31.756 | 33.517
v1 | 33.46 | 32.072 | 31.522 | 33.153
v1 | 34.72 | 31.875 | 31.318 | 32.763
v1 | 35.99 | 31.641 | 31.144 | 32.439
v1 | 37.25 | 31.389 | 30.992 | 32.115
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
