LauanMath/kaelix-firmware/experiments/figures/output/fig7_gateway.png

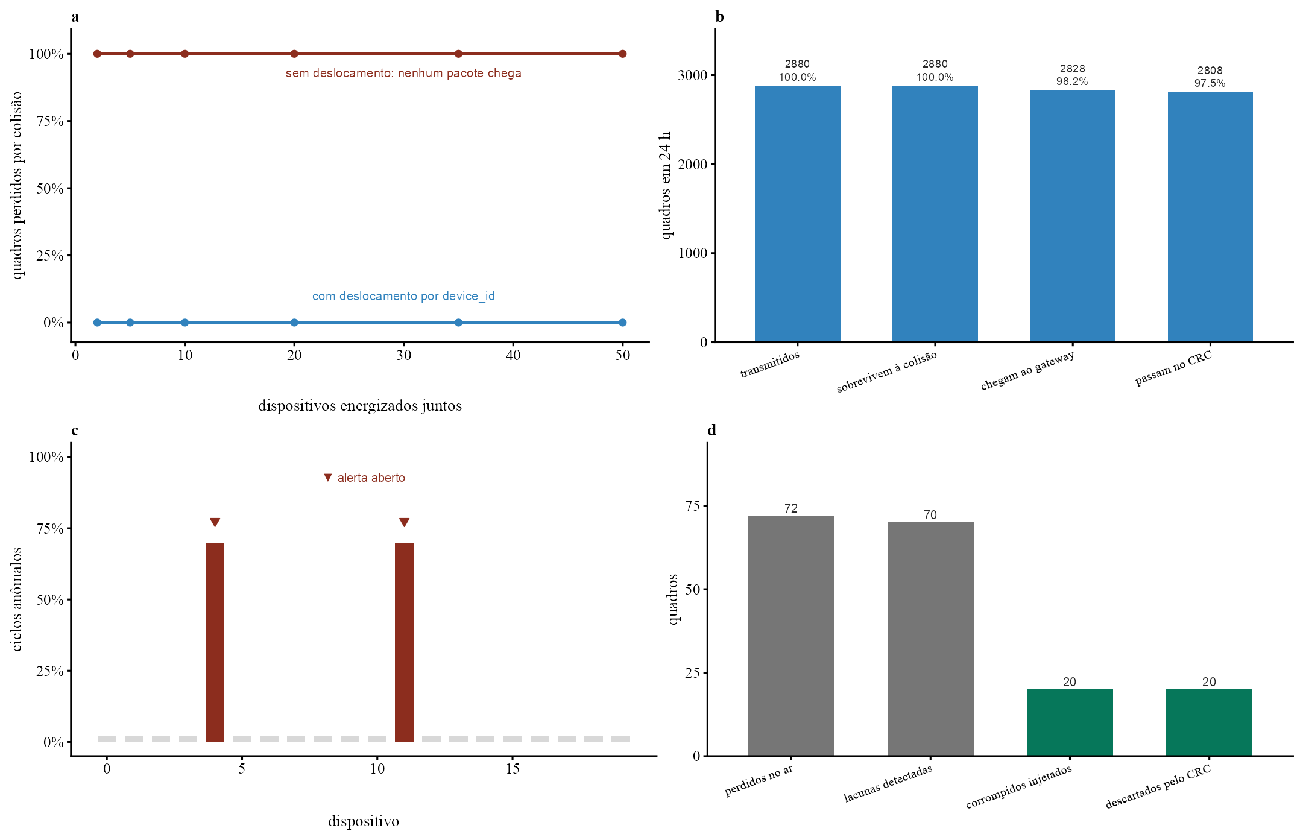
experiments/figures/output/fig7_gateway.png
