LauanMath/kaelix-firmware/experiments/figures/output/fig7_gateway.tiff

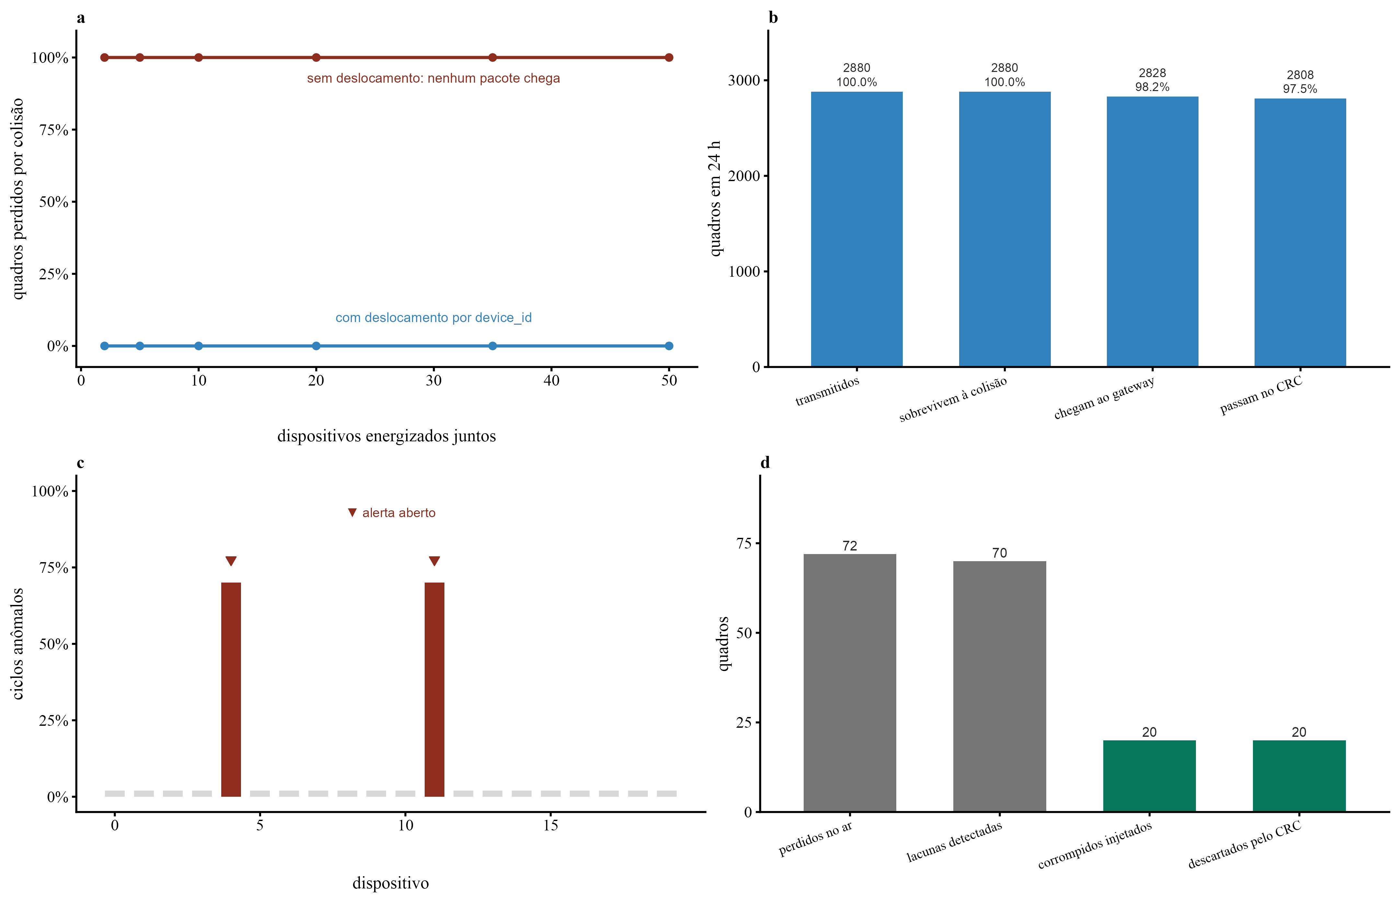
experiments/figures/output/fig7_gateway.tiff
