LauanMath/kaelix-firmware/experiments/figures/output/fig8_circuito.png

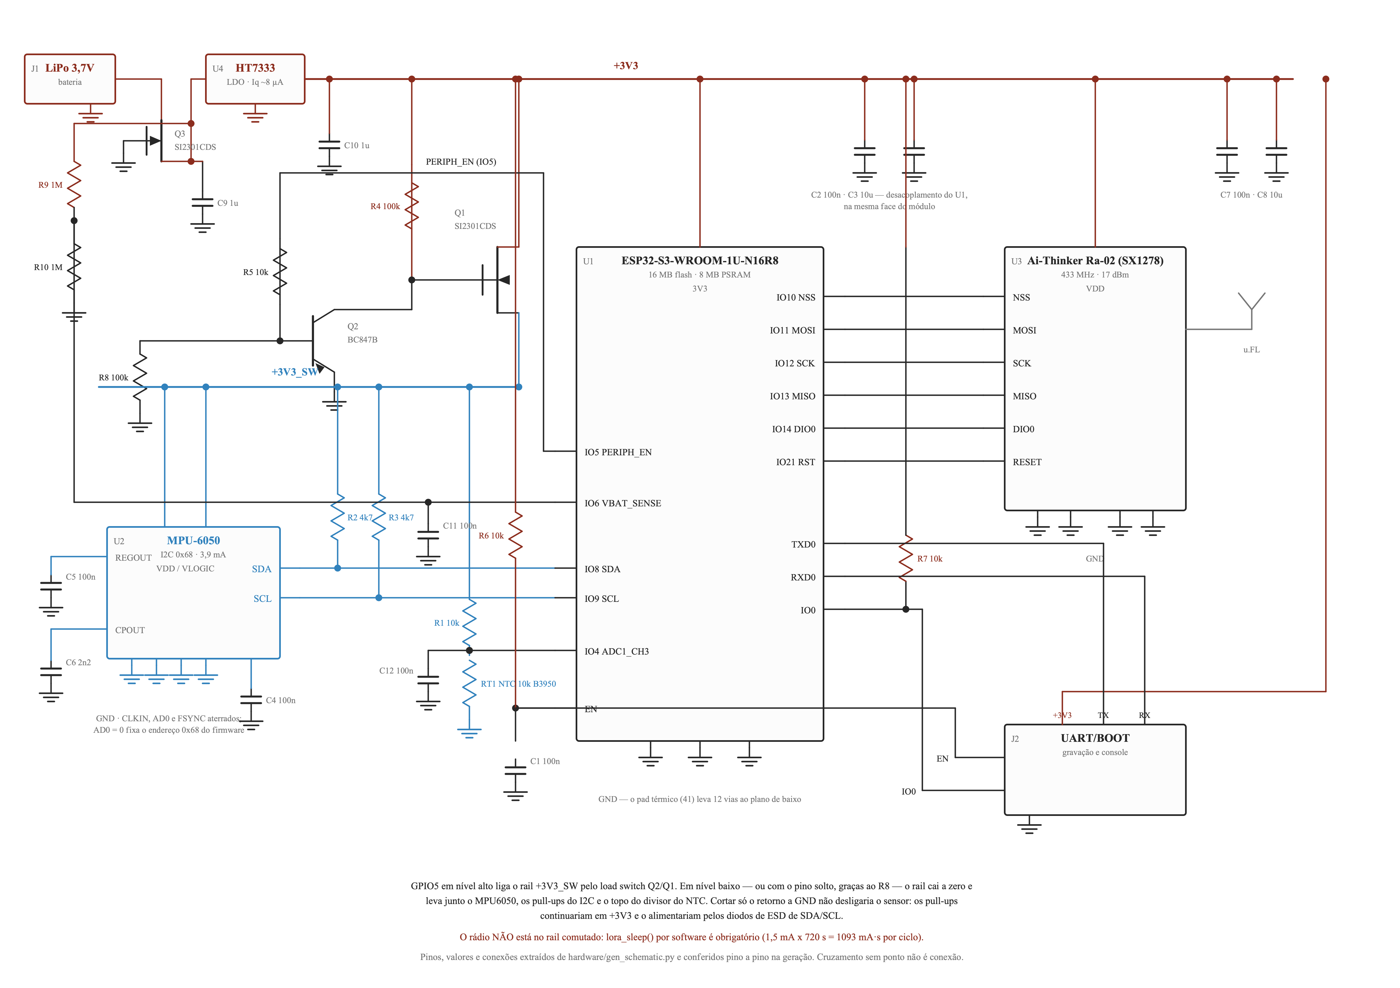
experiments/figures/output/fig8_circuito.png
