LauanMath/kaelix-firmware/docs/device/IMG_5298.jpeg

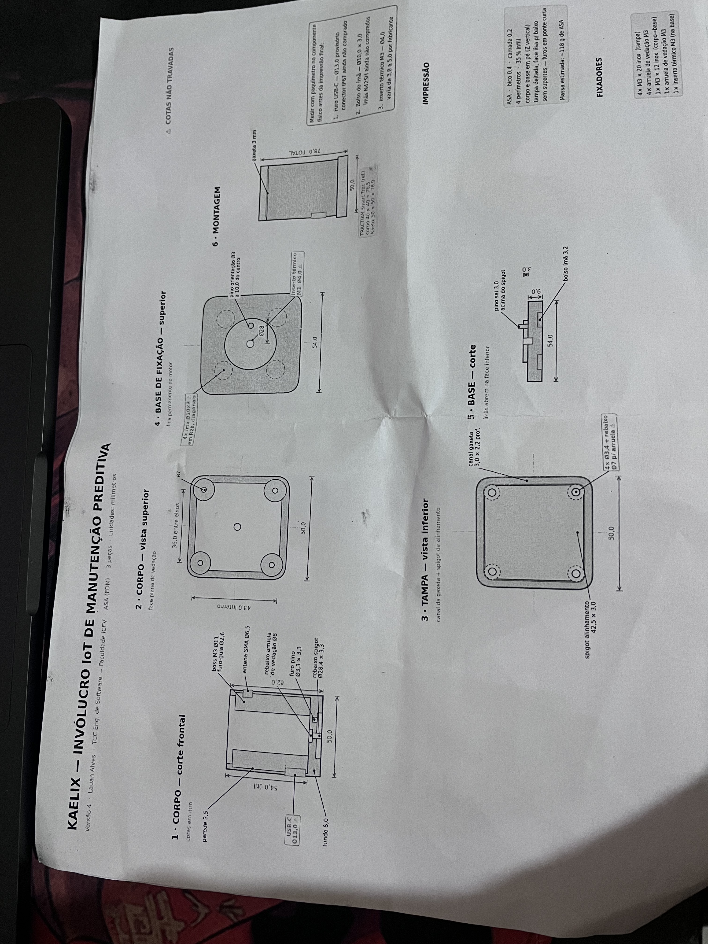
docs/device/IMG_5298.jpeg
